gilleshenrard/leany/firmware/hardware/imu/bmi270/mems_bmi270.c

/*
 * SPDX-FileCopyrightText: 2025 Gilles Henrard <contact@gilleshenrard.com>
 *
 * SPDX-License-Identifier: MIT
 */

/**
 * @file mems_bmi270.c
 * @brief Implement the behavior of the BMI270 MEMS
 *
 * @author Gilles Henrard
 *
 * @details Datasheet : https://www.bosch-sensortec.com/media/boschsensortec/downloads/datasheets/bst-bmi270-ds000.pdf 
 */

#if IMU_MODEL == IMU_BMI270

#include <FreeRTOS.h>  //NOLINT(*-include-cleaner)
#include <bmi270.h>
#include <bmi2_defs.h>
#include <main.h>
#include <portmacro.h>
#include <projdefs.h>
#include <stdint.h>
#include <stm32f103xb.h>
#include <stm32f1xx_hal.h>
#include <stm32f1xx_ll_gpio.h>
#include <stm32f1xx_ll_spi.h>

#include "errorstack.h"
#include "hal_spi.h"
#include "imu.h"
#include "mahony.h"
#include "systick.h"

enum : uint8_t {
    kNBpositionRegisters = 16U,    ///< Number of registers holding Accelerometer and Gyroscope data
    kNBTemperatureRegisters = 2U,  ///< Number of registers holding Temperature data
    kConfigCheckAttempts = 3U,     ///< Maximum number of attempts to re-read a correct config file
};

/**
 * Timings in milliseconds
 */
typedef enum : uint16_t {
    kTimeoutMS = 1000U,           ///< Max number of milliseconds to wait for the device ID
    kConfigTimeoutMS = 20U,       ///< Max number of milliseconds after which the configuration should be ok
    kTemperatureRefreshMS = 10U,  ///< Number of milliseconds between temperature value refreshes
} Timing;

/**
 * Enumeration of the IDs of the functions used by the BMI270 implementation
 */
typedef enum : uint8_t {
    kBMI270readRegisters = 2,        ///< readRegisters() : Function reading several registers
    kBMI270writeRegisters = 3,       ///< burstWriteRegisters() : Function writing multiple registers
    kBMI270stateStartup = 4,         ///< stateStartup() : State in which the startup time is waited for
    kBMI270stateInitialising = 5,    ///< stateInitialising() : State in which the BMI270 is being initialised
    kBMI270checkCommunication = 7,   ///< checkSPICommunication() : Check the SPI communication with the BMI270
    kBMI270checkConfiguration = 8,   ///< checkConfigurationFile() : Check if written configuration file is correct
    kBMI270stateConfiguring = 9,     ///< stateConfiguring() : State in which the BMI270 is configured for the app.
    kBMI270stateMeasuring = 10,      ///< stateMeasuring() : State in which measurements are received from the BMI270
    kBMI270readTemperature = 11,     ///< readTemperature() : Function reading the BMI270 internal temp. registers
    kBMI270stateSelfTestAccel = 12,  ///< stateSelfTestingAccelerometer() : State in which the chip self-tests the acc.
    kBMI270stateSelfTestGyro = 13,   ///< stateSelfTestingGyro() : State in which the BMI270 self-tests the gyroscope
    kBMI270runAccelSelfTest = 14,    ///< runAccelerometerSelfTest() : Run the self-test command on the BMI270
    kBMI270configureRegisters = 15,  ///< configureRegisters() : Write an array of register number/value pairs
    kIMUsoftReset = 16,              ///< IMUsoftReset() function
} FunctionCode;

/**
 * @brief Union regrouping 8-bits and 16-bits arrays
 * @details
 *  This allows reading all the accelerometer and gyroscope values at once, and convert them to 16 bit instantly
 */
typedef union {
    uint8_t registers8bits[kNBpositionRegisters];                   ///< 8-bits registers array
    int16_t values16bits[((uint8_t)(kNBpositionRegisters) >> 1U)];  ///< 16-bits values array
} RawValues;

_Static_assert(((uint8_t)kNBpositionRegisters & (kNBpositionRegisters - 1U)) == 0,
               "NB_POSITION_REGISTERS must be an even number");

typedef uint8_t BMI270register;  ///< type definition for BMI270 registers

// Read/Write bit value
static constexpr uint16_t kConfigFileSize = 8192U;         ///< Size of the config file in bytes
static constexpr BMI270register kBMIwrite = 0x00U;         ///< Address byte value for a write operation
static constexpr BMI270register kBMIread = 0x80U;          ///< Address byte value for a read operation
const uint32_t kMaxSensorTimeTicks = 0xFFFFFFU;            ///< The maximum tick value before it wraps around to 0
const float kSensorTimeResolutionSeconds = 0.0000390625F;  ///< How many seconds a tick lasts

// Utility functions
static ErrorCode writeConfigurationFile(void);
static ErrorCode checkConfigurationFile(void);
static ErrorCode readTemperature(float* temperature_celsius);
static ErrorCode runAccelerometerSelfTest(RawValues* values_read, uint8_t positive_sign);
static inline uint32_t toTicks(const uint8_t registers[3]);
static void applyTemperatureDrift(float temperature_celcius, float accelerometer_g[3], float gyroscope_radps[3]);

/**
 * Accelerometer nominal sensitivity ratio from LSB to G, at +-2G range and 25°C
 * @details Equation :
 * Value(G) = Value(LSB) / 16384(LSB/G)
 *
 * See datasheet p. 12, section "Sensitivity"
 */
static constexpr float kNominalAccelLSBto2G = (1.0F / (float)BMI2_ACC_FOC_2G_REF);

/**
 * Accelerometer nominal sensitivity ratio from LSB to G, at +-16G range and 25°C
 * @details Equation :
 * Value(G) = Value(LSB) / 2048(LSB/G)
 *
 * See datasheet p. 12, section "Sensitivity"
 */
static constexpr float kNominalAccelLSBto16G = (1.0F / (float)BMI2_ACC_FOC_16G_REF);

/**
 * Gyroscope nominal sensitivity ratio from LSB to rad/s, at +-125°/s range and 25°C
 * @details Equation :
 * Value(rad/s) = (Value(LSB) / 262,144(LSB/dps)) * (PI/180°)
 *
 * See datasheet p. 14, section "Sensitivity"
 */
static constexpr float kNominalGyroLSBtoRadps = (1.0F / 262.144F) * 0.017453293F;

/**
 * Accelerometer temperature drift in [%/K], divided by 100 because percents
 */
static constexpr float kAccelTemperatureDriftPercentPerKelvin = (0.004F / 100.0F);

/**
 * Gyroscope temperature drift in [%/K], divided by 100 because percents
 */
static constexpr float kGyroTemperatureDriftPercentPerKelvin = (0.02F / 100.0F);

/**
 * Temperature in [°C] at which the internal temperature value read is 0x0000
 */
static constexpr float kReferenceTemperatureCelsius = 23.0F;

//external variables
extern const uint8_t bmi270_config_file[];  ///< BMI270 config file provided by Bosch Sensortec, declared in bmi270.c

//state variables
static uint8_t configfile_written = 0;  ///< Flag used to ensure config is written only once after reset
static ErrorCode result;                ///< Variable used to store error codes
static SPI spi_descriptor = {.handle = SPI1,
                             .cs_port = IMU_CS_GPIO_Port,
                             .pin = IMU_CS_Pin,
                             .highest_register_number = (BMI2_CMD_REG_ADDR + 1U),
                             .read_mask = kBMIread,
                             .write_mask = kBMIwrite,
                             .read_dummy = 1};  ///< Descriptor of the SPI port used

/****************************************************************************************************************/
/****************************************************************************************************************/

/**
 * Check whether the correct device ID can be retrieved
 *
 * @retval 0 Success
 * @retval 1 Error while reading the BMI270_CHIP_ID register
 * @retval 2 Incorrect device ID
 */
ErrorCode IMUcheckDeviceID(void) {
    BMI270register device_id = 0;

    LL_SPI_Enable(spi_descriptor.handle);

    //attempt to read a correct device ID for max. 1 second
    uint32_t first_tick = getCurrentTick();
    do {
        //store the bitwise-NOT value of the chip ID to make sure every bit is changed by the read command
        device_id = (BMI270register) ~((BMI270register)BMI270_CHIP_ID);

        //read the register
        result = readRegisters(&spi_descriptor, BMI2_CHIP_ID_ADDR, &device_id, 1);
        EXIT_ON_ERROR(result, kBMI270checkCommunication, 1)
    } while ((device_id != BMI270_CHIP_ID) && !systickTimeout(first_tick, kTimeoutMS));

    //check the device ID
    if (device_id != BMI270_CHIP_ID) {
        return (createErrorCode(kBMI270checkCommunication, 2, kErrorCritical));
    }

    return kSuccessCode;
}

/**
 * Request the IMU soft reset
 *
 * @retval 0 Success
 * @retval 1 Error while requesting the soft reset
 * @retval 2 Error while disabling the advanced power mode
 */
ErrorCode IMUsoftReset(void) {
    //issue a soft reset command to reset all registers to their default value
    // (useful when debugging and the supply voltage is not interrupted)
    BMI270register value = BMI2_SOFT_RESET_CMD;
    result = writeRegisters(&spi_descriptor, BMI2_CMD_REG_ADDR, &value, 1);
    EXIT_ON_ERROR(result, kIMUsoftReset, 1)

    //Disable advanced power mode
    value = 0x00;
    result = writeRegisters(&spi_descriptor, BMI2_PWR_CONF_ADDR, &value, 1);
    EXIT_ON_ERROR(result, kIMUsoftReset, 2)

    //Getting out of advanced power mode takes up to 450us
    vTaskDelay(pdMS_TO_TICKS(1U));

    configfile_written = 0;
    return kSuccessCode;
}

/**
 * State in which the BMI270 self-tests the accelerometer
 *
 * @details This follows the procedure descripted in the datasheet :
 * https://www.bosch-sensortec.com/media/boschsensortec/downloads/datasheets/bst-bmi270-ds000.pdf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
 * 
 * @retval 0 Success
 * @retval 1 Error while writing preliminary self-test configuration
 * @retval 2 Error while performing the positive-sign self-test
 * @retval 3 Error while performing the negative-sign self-test
 * @retval 4 Error while disabling the self-test
 * @retval 5 Self-test value deltas do not match the ones stated in the datasheet
 */
ErrorCode selfTestAccelerometer(void) {
    const BMI270register accel_range_register_number = 0x41U;  ///< Accelerometer range value register number
    BMI270register value = 0;

    const BMI270register configuration[][2] = {
        // NOLINTBEGIN(*-signed-bitwise)
        {BMI2_PWR_CTRL_ADDR, BMI2_ACC_EN_MASK},             //enable accelerometer
        {accel_range_register_number, BMI2_ACC_RANGE_16G},  //set the accel. range to +-16G
        {BMI2_ACC_SELF_TEST_ADDR, (1U << (uint8_t)BMI2_ACC_SELF_TEST_AMP_POS)},
        {BMI2_ACC_CONF_ADDR, (1U << BMI2_ACC_FILTER_PERF_MODE_POS) |
                                 (BMI270register)(BMI2_ACC_NORMAL_AVG4 << BMI2_ACC_BW_PARAM_POS) | BMI2_ACC_ODR_1600HZ},
        // NOLINTEND(*-signed-bitwise)
    };

    //send the configuration array
    const uint8_t nb_registers = sizeof(configuration) / 2;
    result = writeRegistersBunch(&spi_descriptor, configuration, nb_registers);
    EXIT_ON_ERROR(result, kBMI270stateSelfTestAccel, 1)

    //wait for 2ms
    vTaskDelay(pdMS_TO_TICKS(2U));

    RawValues lsb_posivite = {0};  ///< Buffer holding the LSB values read from the IC
    RawValues lsb_negative = {0};  ///< Buffer holding the LSB values read from the IC

    result = runAccelerometerSelfTest(&lsb_posivite, 1);
    EXIT_ON_ERROR(result, kBMI270stateSelfTestAccel, 2)

    result = runAccelerometerSelfTest(&lsb_negative, 0);
    EXIT_ON_ERROR(result, kBMI270stateSelfTestAccel, 3)

    //disable self-testing
    value = 0x00;
    result = writeRegisters(&spi_descriptor, BMI2_ACC_SELF_TEST_ADDR, &value, 1U);
    EXIT_ON_ERROR(result, kBMI270stateSelfTestAccel, 4)

    //transform the values read to values in [G] (9.81 m/s²)
    const float delta_x_g =
        (float)(lsb_posivite.values16bits[kXaxis] - lsb_negative.values16bits[kXaxis]) * kNominalAccelLSBto16G;
    const float delta_y_g =
        (float)(lsb_posivite.values16bits[kYaxis] - lsb_negative.values16bits[kYaxis]) * kNominalAccelLSBto16G;
    const float delta_z_g =
        (float)(lsb_posivite.values16bits[kZaxis] - lsb_negative.values16bits[kZaxis]) * kNominalAccelLSBto16G;

    //check if the minimum delta given in the datasheet is respected
    const float min_delta_x_g = 16.0F;
    const float min_delta_y_g = -15.0F;
    const float min_delta_z_g = 10.0F;
    if ((delta_x_g <= min_delta_x_g) || (delta_y_g >= min_delta_y_g) || (delta_z_g <= min_delta_z_g)) {
        return createErrorCode(kBMI270stateSelfTestAccel, 5, kErrorCritical);  // NOLINT(*-magic-numbers)
    }

    return kSuccessCode;
}

/**
 * State in which the BMI270 self-tests the gyroscope
 *
 * @details This follows the procedure descripted in the datasheet :
 * https://www.bosch-sensortec.com/media/boschsensortec/downloads/datasheets/bst-bmi270-ds000.pdf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
 * 
 * @retval 0 Success
 * @retval 1 Error while requesting the self-test triggering
 * @retval 2 Error while reading the self-test result
 * @retval 3 Error while reading the self-test error code
 * @retval 4 Gyroscope self-test internal error @note Internal error code stored one layer lower
 */
ErrorCode selfTestGyroscope(void) {
    BMI270register value = 0;

    //set the gyro self-test trigger command
    value = BMI2_G_TRIGGER_CMD;
    result = writeRegisters(&spi_descriptor, BMI2_CMD_REG_ADDR, &value, 1);
    EXIT_ON_ERROR(result, kBMI270stateSelfTestGyro, 1)

    //wait for the self-test done flag
    uint32_t start_tick = getCurrentTick();
    do {
        result = readRegisters(&spi_descriptor, BMI2_GYR_SELF_TEST_AXES_ADDR, &value, 1);
    } while (!isError(result) && !systickTimeout(start_tick, kTimeoutMS) &&
             ((value & (uint8_t)BMI2_ACC_SELF_TEST_DONE_MASK) != BMI2_ACC_SELF_TEST_DONE_MASK));

    EXIT_ON_ERROR(result, kBMI270stateSelfTestGyro, 2)

    //check if all axis are flagged as ok
    const BMI270register gyro_gain_status_registernumber = 0x38;
    const BMI270register all_gyroscope_ok =
        (BMI2_ACC_X_OK_MASK | BMI2_ACC_Y_OK_MASK | BMI2_ACC_Z_OK_MASK |  // NOLINT(*-signed-bitwise)
         BMI2_ACC_SELF_TEST_DONE_MASK);                                  // NOLINT(*-signed-bitwise)
    if ((value & all_gyroscope_ok) != all_gyroscope_ok) {
        BMI270register trigger_status = 0;
        result = readRegisters(&spi_descriptor, gyro_gain_status_registernumber, &trigger_status, 1);
        EXIT_ON_ERROR(result, kBMI270stateSelfTestGyro, 3)

        result = createErrorCodeLayer1(kBMI270stateSelfTestGyro, value, trigger_status, kErrorCritical);
        return pushErrorCode(result, kBMI270stateSelfTestGyro, 4);  // NOLINT(*-magic-numbers)
    }

    return kSuccessCode;
}

/**
 * Write the BMI270 config file
 * @attention This is to be done only once after Power On Reset
 *
 * @retval 0 Success
 * @retval 1 Error while starting the config file load
 * @retval 2 Error while writing the config file
 * @retval 3 Error while ending the config file load
 * @retval 4 Error while requesting the BMI270 status
 * @retval 5 BMI270 status error
 */
ErrorCode IMUinitialise(void) {
    //make sure config file is written only once after POR or soft reset
    if (configfile_written) {
        return kSuccessCode;
    }

    const BMI270register start_configfile_load = 0x00U;
    const BMI270register finish_configfile_load = 0x01U;

    //Request configuration start
    BMI270register value = start_configfile_load;
    result = writeRegisters(&spi_descriptor, BMI2_INIT_CTRL_ADDR, &value, 1);
    EXIT_ON_ERROR(result, kBMI270stateInitialising, 1)

    result = writeConfigurationFile();
    EXIT_ON_ERROR(result, kBMI270stateInitialising, 2)

    //Request configuration finish
    value = finish_configfile_load;
    result = writeRegisters(&spi_descriptor, BMI2_INIT_CTRL_ADDR, &value, 1);
    EXIT_ON_ERROR(result, kBMI270stateInitialising, 3)

    //Applying the new config takes up to 20ms
    vTaskDelay(pdMS_TO_TICKS(kConfigTimeoutMS));

    //Wait for the initialisation status register to show a success or an error
    uint32_t config_start_tick = getCurrentTick();
    do {
        result = readRegisters(&spi_descriptor, BMI2_INTERNAL_STATUS_ADDR, &value, 1);
        EXIT_ON_ERROR(result, kBMI270stateInitialising, 4)
    } while ((value == BMI2_NOT_INIT) && !systickTimeout(config_start_tick, kConfigTimeoutMS));

    //check if an initialisation error occurred
    if (value != BMI2_INIT_OK) {
        return createErrorCodeLayer1(kBMI270stateInitialising, 5, value, kErrorCritical);  // NOLINT(*-magic-numbers)
    }

    configfile_written = 1;
    return kSuccessCode;
}

/**
 * Configure the BMI270 registers for this application
 *
 * @retval 0 Success
 * @retval 1 Error while writing the configuration registers
 */
ErrorCode IMUconfigure(void) {
    const BMI270register accel_range_register_number = 0x41U;  ///< Accelerometer range value register number
    const BMI270register gyro_range_register_number = 0x43U;   ///< Gyroscope range value register number
    const BMI270register no_fifo = 0x00;                       ///< Value used to disable the FIFO

    const BMI270register configuration[][2] = {
        // NOLINTBEGIN(*-signed-bitwise)
        {BMI2_PWR_CTRL_ADDR,
         (BMI2_GYR_EN_MASK | BMI2_ACC_EN_MASK | BMI2_TEMP_EN_MASK)},  //enable temp, gyroscope and accel.
        {BMI2_ACC_CONF_ADDR, (BMI2_ACC_FILTER_PERF_MODE_MASK | (BMI2_ACC_CIC_AVG8 << 4U) | BMI2_ACC_ODR_1600HZ)},  //
        {accel_range_register_number, BMI2_ACC_RANGE_2G},  //set the accel. range to +-2G
        {BMI2_GYR_CONF_ADDR, (BMI2_GYR_FILTER_PERF_MODE_MASK | BMI2_GYR_NOISE_PERF_MODE_MASK |
                              (BMI2_GYR_NORMAL_MODE << 4U) | BMI2_GYR_ODR_1600HZ)},
        {gyro_range_register_number, BMI2_GYR_RANGE_125},  //set the gyroscope range to +-500°/s
        {BMI2_FIFO_CONFIG_1_ADDR, no_fifo},                //disable the FIFO (streaming mode)
        {BMI2_INT_MAP_DATA_ADDR, BMI2_DRDY_INT},           //enable Data Ready interrupt on INT1
        {BMI2_INT1_IO_CTRL_ADDR, BMI2_INT_OUTPUT_EN_MASK | BMI2_INT_OPEN_DRAIN_MASK |
                                     BMI2_INT_LEVEL_MASK},  //enable INT1 active high, open drain
        {BMI2_PWR_CONF_ADDR, 0x00},                         //disable advanced power mode
        // NOLINTEND(*-signed-bitwise)
    };

    //send the configuration array
    result = writeRegistersBunch(&spi_descriptor, configuration, (sizeof(configuration) / sizeof(configuration)[0]));
    EXIT_ON_ERROR(result, kBMI270stateConfiguring, 1)

    return kSuccessCode;
}

/**
 * Initialise the time fields of the Mahony filter's context
 *
 * @param[out] filter_context Mahony filter's current context
 */
void IMUsetupTimebase(MahonyContext* filter_context) {
    filter_context->dt.max_tick = kMaxSensorTimeTicks;
    filter_context->dt.tick_period_seconds = kSensorTimeResolutionSeconds;
}

/**
 * Get the latest IMU sample
 *
 * @param[out] sample Sample to gather
 * @retval 0 Success
 * @retval 1 Error while reading the sample registers
 * @retval 2 Error while reading the chip temperature
 */
ErrorCode IMUgetSample(IMUsample* sample) {
    RawValues lsb_values = {0};        ///< Buffer holding the LSB values read from the IC
    float temperature_celsius = 0.0F;  ///< Latest internal temperature in [°C]

    //read all accelerometer/gyroscope values
    result = readRegisters(&spi_descriptor, BMI2_ACC_X_LSB_ADDR, lsb_values.registers8bits, kNBpositionRegisters);
    EXIT_ON_ERROR(result, kBMI270stateMeasuring, 1)

    //apply the nominal sensitivity to the measurements to change them to usable units
    for (uint8_t axis = 0; axis < (uint8_t)kNBaxis; axis++) {
        sample->accelerometer_g[axis] = (float)(lsb_values.values16bits[axis]) * kNominalAccelLSBto2G;
        sample->gyroscope_radps[axis] = (float)(lsb_values.values16bits[axis + kNBaxis]) * kNominalGyroLSBtoRadps;
    }

    //read the BMI270 temperature every 10ms
    static TickType_t latest_temperature_tick = 0;
    if (systickTimeout(latest_temperature_tick, kTemperatureRefreshMS)) {
        latest_temperature_tick = getCurrentTick();

        result = readTemperature(&temperature_celsius);
        EXIT_ON_ERROR(result, kBMI270stateMeasuring, 2)
    }

    //take temperature drift into account with sensitivity
    applyTemperatureDrift(temperature_celsius, sample->accelerometer_g, sample->gyroscope_radps);

    //update the current sensor time ticks
    const uint8_t nb_measure_registers = (uint8_t)kNBaxis << 2U;
    sample->tick = toTicks(&lsb_values.registers8bits[nb_measure_registers]);

    return kSuccessCode;
}

/**
 * Get the number of samples to ignore after configuration
 *
 * @return 0 
 */
uint8_t getNbSamplesToIgnore(void) { return 0; }

/****************************************************************************************************************/
/****************************************************************************************************************/

/**
 * Write the configuration file to the BMI270 and check it is correct
 *
 * @retval 0 Success
 * @retval 1 Error while writing the config file
 * @retval 2 The Config file was not written correctly
 */
static ErrorCode writeConfigurationFile(void) {
    //Write the config file provided by Bosch Sensortec
    result = writeRegisters(&spi_descriptor, BMI2_INIT_DATA_ADDR, bmi270_config_file, kConfigFileSize);
    EXIT_ON_ERROR(result, kBMI270stateInitialising, 1)

    //re-read the configuration file written to make sure it is correct (max. 3 attempts)
    uint8_t attempts = kConfigCheckAttempts;
    do {
        result = checkConfigurationFile();
    } while ((--attempts) && isError(result));
    EXIT_ON_ERROR(result, kBMI270stateInitialising, 2)

    return result;
}

/**
 * Read the configuration file stored in the BMI270 and make sure it corresponds to the one provided by Bosch
 * 
 * @retval 0 Success
 * @retval 1 Timeout while reading the configuration file
 * @retval 2 Data difference between configuration files
 */
static ErrorCode checkConfigurationFile(void) {
    const uint8_t spi_rx_filler = 0xFFU;  ///< Value to send as a filler while receiving multiple bytes

    //set timeout timer and enable CS
    uint32_t spi_start_tick = getCurrentTick();
    LL_GPIO_ResetOutputPin(IMU_CS_GPIO_Port, IMU_CS_Pin);

    //send the config data read request and receive a dummy byte
    (void)receiveSPIbyte(&spi_descriptor, BMI2_INIT_DATA_ADDR, spi_start_tick);
    (void)receiveSPIbyte(&spi_descriptor, spi_rx_filler, spi_start_tick);

    //receive the bytes to read
    uint8_t failure = 0;
    uint16_t byte_index = 0;
    do {
        BMI270register value = receiveSPIbyte(&spi_descriptor, spi_rx_filler, spi_start_tick);
        failure = (value != bmi270_config_file[byte_index]);
        byte_index++;
    } while (!failure && (byte_index < kConfigFileSize) && !systickTimeout(spi_start_tick, kSPItimeoutMS));

    //wait for transaction to be finished and clear Overrun flag
    while (LL_SPI_IsActiveFlag_BSY(spi_descriptor.handle) && !systickTimeout(spi_start_tick, kSPItimeoutMS)) {
    };
    LL_SPI_ClearFlag_OVR(spi_descriptor.handle);

    //disable CS
    LL_GPIO_SetOutputPin(IMU_CS_GPIO_Port, IMU_CS_Pin);

    //if timeout, error
    if (systickTimeout(spi_start_tick, kSPItimeoutMS)) {
        return (createErrorCode(kBMI270checkConfiguration, 1, kErrorWarning));
    }

    if (failure || (byte_index < kConfigFileSize)) {
        return (createErrorCode(kBMI270checkConfiguration, 2, kErrorWarning));
    }

    return kSuccessCode;
}

/**
 * Read the BMI270 internal temperature
 * 
 * @param[out] temperature_celsius Temperature in [°C] to update if the temperature read is valid
 * @retval 0 Success
 * @retval 1 Error while reading the registers
 */
static ErrorCode readTemperature(float* temperature_celsius) {
    int16_t read_buffer = 0x0000;

    //read temperature value
    result = readRegisters(&spi_descriptor, BMI2_TEMPERATURE_0_ADDR, (uint8_t*)&read_buffer, kNBTemperatureRegisters);
    EXIT_ON_ERROR(result, kBMI270readTemperature, 1)

    //check if the temperature LSB read is valid
    const int16_t invalid_temperature_lsb = (int16_t)0x8000;
    if (read_buffer == invalid_temperature_lsb) {
        return kSuccessCode;
    }

    //transform temperature LSB to °C
    const float kelvin_per_lsb = 0.001953125F;
    *temperature_celsius = kReferenceTemperatureCelsius + ((float)read_buffer * kelvin_per_lsb);

    return kSuccessCode;
}

/**
 * Send the self-test request to the BMI270 and read its results
 * 
 * @param[out] values_read Buffer to which save the read self-test values 
 * @param positive_sign 1 if self-test sign is positive, 0 if negative
 * @retval 0 Success
 * @retval 1 Error while sending the self-test request
 * @retval 2 Error while reading the self-test results
 */
static ErrorCode runAccelerometerSelfTest(RawValues* values_read, uint8_t positive_sign) {
    //prepare the register value to write to start the self-testing
    BMI270register value = (uint8_t)(positive_sign << (uint8_t)BMI2_ACC_SELF_TEST_SIGN_POS);
    value |= (1U << (uint8_t)BMI2_ACC_SELF_TEST_AMP_POS);
    value |= (uint8_t)BMI2_ACC_SELF_TEST_EN_MASK;

    //write the self-test request and wait for it to finish
    result = writeRegisters(&spi_descriptor, BMI2_ACC_SELF_TEST_ADDR, &value, 1U);
    EXIT_ON_ERROR(result, kBMI270runAccelSelfTest, 1)
    vTaskDelay(pdMS_TO_TICKS(51U));

    //read all accelerometer/gyroscope values
    result = readRegisters(&spi_descriptor, BMI2_ACC_X_LSB_ADDR, values_read->registers8bits, kNBpositionRegisters);
    EXIT_ON_ERROR(result, kBMI270runAccelSelfTest, 2)

    return kSuccessCode;
}

/**
 * Assemble sensor time registers into tick value
 *
 * @param registers Sensor time registers
 * @return Tick value
 */
static inline uint32_t toTicks(const uint8_t registers[3]) {
    return (registers[0] | (uint32_t)(registers[1U] << 8U)  //NOLINT (*-magic-numbers)
            | (uint32_t)(registers[2] << 16U));             //NOLINT (*-magic-numbers)
}

/**
 * Apply temperature drifts to the measurements
 *
 * @param temperature_celcius Internal temperature in [°C]
 * @param[out] accelerometer_g Accelerometer values in [G] (9.81 m/s²)
 * @param[out] gyroscope_radps Gyroscope values in [rad/s]
 */
//NOLINTNEXTLINE(bugprone-easily-swappable-parameters)
static void applyTemperatureDrift(const float temperature_celcius, float accelerometer_g[3], float gyroscope_radps[3]) {
    const float delta_celsius = temperature_celcius - kReferenceTemperatureCelsius;
    const float accel_drift_percent = (delta_celsius * kAccelTemperatureDriftPercentPerKelvin);
    const float gyro_drift_percent = (delta_celsius * kGyroTemperatureDriftPercentPerKelvin);

    for (uint8_t axis = 0; axis < (uint8_t)kNBaxis; axis++) {
        accelerometer_g[axis] += (accel_drift_percent * accelerometer_g[axis]);
        gyroscope_radps[axis] += (gyro_drift_percent * gyroscope_radps[axis]);
    }
}
#endif
