gilleshenrard/leany/firmware/tasks/task_battery.c

/**
 * SPDX-FileCopyrightText: 2026 Gilles Henrard <contact@gilleshenrard.com>
 * SPDX-License-Identifier: MIT
 *
 * @file task_battery.c
 * @brief Implement the battery voltage and charger status monitoring
 * @author Gilles Henrard
 */
#include "task_battery.h"

#include <FreeRTOS.h>
#include <FreeRTOSConfig.h>
#include <assert.h>
#include <main.h>
#include <portmacro.h>
#include <projdefs.h>
#include <semphr.h>
#include <stdint.h>
#include <stm32f103xb.h>
#include <stm32f1xx_ll_i2c.h>
#include <task.h>

#include "bq25619.h"
#include "bq25619_registers.h"
#include "errorstack.h"
#include "hal_adc.h"
#include "hal_i2c.h"
#include "hardware_events.h"
#include "systick.h"
#include "task_gpio.h"

enum : uint16_t {
    kStackSize_words = 110U,         ///< Amount of words in the task stack
    kTaskLowPriority = 3U,           ///< FreeRTOS number for a low priority task
    kNbChipIDtests = 5U,             ///< Number of times chip ID reading must be tested
    kBatteryFullPercent = 100U,      ///< Value used as a 100% battery level
    kNbRetries = 5U,                 ///< Maximum number of retries upon I²C lack of ACK
    kNbAverageSamples = 16U,         ///< Maximum number of elements in the average buffer
    kAdcMaxValue = 4095U,            ///< Maximum ADC LSB value (12-bits -> [0 ... 4095])
    kBatteryMaxMv = 4200U,           ///< Maximum voltage of a typical lithium cell in [mV]
    kBatteryMinMv = 3500U,           ///< Minimum voltage of a typical lithium cell in [mV]
    kBatteryMinDetectionMv = 2500U,  ///< Minimum voltage detection threshold in [mV]
    kNbBatteryLevelSteps = 21U,      ///< Number of battery level steps in the lookup table
    kBatteryLevelPercentStep = 5U,   ///< Number of percents between two steps
};

static_assert(((uint8_t)kNbAverageSamples & ((uint8_t)kNbAverageSamples - 1U)) == 0U,
              "kNbAverageSamples must be a power of 2");

/**
 * Timings in milliseconds
 */
typedef enum : uint16_t {
    kBatteryLvlUpdatePeriodMs = 1000U,  ///< Period in [ms] between two battery level updates
    kMutexTimeoutMs = 10U,              ///< Maximum number of milliseconds before considering a mutex timeout
    kChipIDtimeout = 1000U,             ///< Maximum number of milliseconds to attempt reading the chip ID
    kUpdatePeriodMS = 200U,             ///< Period between two status updates in [ms]
    kMutexMS = 5U,                      ///< Max number of milliseconds to wait for a mutex
} Timing;

/**
 * @brief Enumeration of all the function ID used in errors
 */
typedef enum : uint8_t {
    kTaskLoop = 1,          ///< taskBatteryManagement() function
    kStateStartup = 3,      ///< stateStartup() state function
    kStateIdle = 4,         ///< stateIdle() state function
    kRequestRead = 5,       ///< requestRead() function
    kStateConfiguring = 8,  ///< stateConfiguring() state function
} FunctionCode;

//state machine functions
static void taskBatteryManagement(void* argument);
static ErrorCode stateStartup(void);
static ErrorCode stateConfiguring(void);
static ErrorCode stateIdle(void);
static void updateBatteryVoltage(void);
static uint16_t adcToBatteryVoltage_mV(uint16_t adc_raw, uint32_t adc_vref_mv);
static void averageBatteryVoltageMv(uint32_t new_voltage_mv);
static uint8_t batteryVoltageToPercent(uint32_t voltage_mv);

/**
 * Lookup table mapping SoC level (in 5% steps) to cell voltage (mV).
 *
 * Index 0  = 0%   SoC = 3500 mV  (discharge cutoff)
 * Index 20 = 100% SoC = 4200 mV  (fully charged)
 *
 * Based on a typical Li-ion 18650 OCV discharge curve at ~80 mA load.
 * Voltage range: 3500 mV to 4200 mV.
 * Step size: 5% SoC per entry.
 */
static constexpr uint16_t kBatteryLevelsLookupTable[kNbBatteryLevelSteps] = {
    kBatteryMinMv,  // 0%
    3520U,          // 5%
    3550U,          // 10%
    3580U,          // 15%
    3610U,          // 20%
    3630U,          // 25%
    3650U,          // 30%
    3670U,          // 35%
    3690U,          // 40%
    3710U,          // 45%
    3730U,          // 50%
    3760U,          // 55%
    3790U,          // 60%
    3820U,          // 65%
    3860U,          // 70%
    3910U,          // 75%
    3970U,          // 80%
    4030U,          // 85%
    4090U,          // 90%
    4150U,          // 95%
    kBatteryMaxMv,  // 100%
};

// NOLINTBEGIN (hicpp-use-nullptr)
static volatile TaskHandle_t task_handle = nullptr;              ///< handle of the FreeRTOS task
static volatile FunctionCode state = kStateStartup;              ///< Current state machine state
static StackType_t task_stack[kStackSize_words] = {0};           ///< Buffer used as the task stack
static StaticTask_t task_state = {0};                            ///< Task state variables
static SemaphoreHandle_t battery_mutex = nullptr;                ///< Mutex used to protect the battery status
static ErrorCode result = {0};                                   ///< Buffer used to store the latest error code
static I2C_TypeDef* i2c_handle = I2C1;                           ///< I²C handle to use with all transmissons
static uint8_t battery_percentage = kBatteryFullPercent;         ///< Current battery percentage
static uint8_t previous_battery_percentage = 0;                  ///< Previous battery percentage
static bool battery_charging = false;                            ///< Current battery charge status
static TickType_t previous_tick = 0;                             ///< Tick at the last status update
static ChargerStatus current_battery_status;                     ///< Current battery status flags
static uint32_t last_battery_lvl_update_tick = 0;                ///< Last tick at which battery lvl was updated
static uint32_t battery_average_queue[kNbAverageSamples] = {0};  ///< Buffer used for averaging battery
static uint8_t battery_average_nbsamples = 0;                    ///< Number of samples saved in the buffer
static uint8_t battery_average_index = 0;                        ///< Index of the current buffer head
static uint32_t battery_average_total = 0;                       ///< Total value used to calculate battery average
static uint16_t battery_voltage_mv = 0;                          ///< Current battery voltage in [mV]
// NOLINTEND

/****************************************************************************************************************/
/****************************************************************************************************************/

/**
 * Create the FreeRTOS task which takes care of the battery and charger management
 *
 * @return Success
 */
ErrorCode createBatteryTask(void) {
    // NOLINTBEGIN (hicpp-use-nullptr)
    static StaticSemaphore_t battery_mutex_state = {0};  ///< battery mutex state variables
    // NOLINTEND

    //create a semaphore to protect battery status
    battery_mutex = xSemaphoreCreateMutexStatic(&battery_mutex_state);
    configASSERT(battery_mutex);

    //create the static task
    task_handle = xTaskCreateStatic(taskBatteryManagement, "Battery management task", kStackSize_words, nullptr,
                                    kTaskLowPriority, task_stack, &task_state);
    if (!task_handle) {
        Error_Handler();
    }

    return kSuccessCode;
}

/**
 * Get the battery status
 *
 * @param[out] status Battery current status
 * @return Success 
 */
//NOLINTNEXTLINE(bugprone-easily-swappable-parameters)
ErrorCode getBatteryStatus(BatteryStatus* status) {
    if (!status) {
        return createErrorCode(1, 1, kErrorError);
    }

    if (xSemaphoreTake(battery_mutex, pdMS_TO_TICKS(kMutexTimeoutMs)) != pdTRUE) {
        return createErrorCode(1, 2, kErrorError);
    }

    *status = (BatteryStatus){.level_percents = battery_percentage,
                              .charging = (battery_charging || isBQ25619charging(&current_battery_status))};
    xSemaphoreGive(battery_mutex);
    return kSuccessCode;
}

/**
 * Set the battery charge status
 * @param status New status
 */
void setBatteryChargeStatus(bool status) {
    if (xSemaphoreTake(battery_mutex, pdMS_TO_TICKS(kMutexTimeoutMs)) == pdTRUE) {
        battery_charging = status;
        xSemaphoreGive(battery_mutex);
    }
}

/**
 * Turn the system off
 *
 * @return disconnectBattery() code
 */
ErrorCode turnSystemOff(void) { return disconnectBattery(); }

/**
 * Get the latest measured battery voltage
 *
 * @param[out] voltage_mv Battery voltage in [mV]
 * @retval true Successfully retrieved
 * @retval false Could not retrieve voltage
 */
bool getBatteryVoltageMv(uint16_t* voltage_mv) {
    bool success = false;
    if (xSemaphoreTake(battery_mutex, pdMS_TO_TICKS(kMutexMS)) == pdTRUE) {
        *voltage_mv = battery_voltage_mv;
        success = true;
        xSemaphoreGive(battery_mutex);
    }

    return success;
}

/****************************************************************************************************************/
/****************************************************************************************************************/

/**
 * Run the battery management FreeRTOS task
 *
 * @param argument Unused
 */
static void taskBatteryManagement(void* argument) {
    (void)argument;

    LL_I2C_Enable(i2c_handle);

    last_battery_lvl_update_tick = getCurrentTick();
    while (1) {
        switch (state) {
            case kStateStartup:
                result = stateStartup();
                state = kStateConfiguring;
                break;

            case kStateConfiguring:
                result = stateConfiguring();
                previous_tick = getCurrentTick();
                state = kStateIdle;
                break;

            case kStateIdle:
                result = stateIdle();
                break;

            case kTaskLoop:
            case kRequestRead:
            default:
                result = createErrorCode(kTaskLoop, 1, kErrorCritical);
                break;
        }

        if (isError(result)) {
            Error_Handler();
        }
    }
}

/**
 * State during which the charger startup procedure is ran
 *
 * @retval 0 Success
 * @retval 1 Error while reading the chip ID
 * @retval 2 Invalid chip ID
 * @retval 3 Error while resetting the registers to default
 */
static ErrorCode stateStartup(void) {
    result = testBQ25619identifier();
    EXIT_ON_ERROR(result, kStateStartup, 1)

    for (uint8_t attempt = 0; attempt < kNbRetries; attempt++) {
        result = resetBQ25619();
        if (getDeepestError(result) != kErrorAcknowledgeFailure) {
            break;
        }
    }
    EXIT_ON_ERROR(result, kStateStartup, 2)

    vTaskDelay(pdMS_TO_TICKS(5));

    return kSuccessCode;
}

/**
 * State during which the charger's registers are configured
 *
 * @retval 0 Success
 * @retval 1 Error while writing a configuration register
 */
static ErrorCode stateConfiguring(void) {
    for (uint8_t attempt = 0; attempt < kNbRetries; attempt++) {
        result = configureBQ25619();
        if (getDeepestError(result) != kErrorAcknowledgeFailure) {
            break;
        }
    }
    EXIT_ON_ERROR(result, kStateConfiguring, 1)

    return kSuccessCode;
}

/**
 * State during which the state machine is idle
 *
 * @retval 1 Error while reading the status
 * @retval 2 Error while re-reading the status
 */
static ErrorCode stateIdle(void) {
    vTaskDelayUntil(&previous_tick, pdMS_TO_TICKS(kUpdatePeriodMS));

    ChargerStatus changes;

    //retrieve the latest charger status
    for (uint8_t attempt = 0; attempt < kNbRetries; attempt++) {
        result = updateBQ25619status(&current_battery_status, &changes);
        if (getDeepestError(result) != kErrorAcknowledgeFailure) {
            break;
        }
    }
    EXIT_ON_ERROR(result, kStateIdle, 1);

    //if status changed, trigger event
    if (BQ25619statusChanged(&changes)) {
        if (BQ25619Error(&current_battery_status)) {
            return createErrorCode(kStateIdle, 2, kErrorError);
        }
        triggerHardwareEvent(kEventBatteryStatus);
    }

    updateBatteryVoltage();

    uint16_t battery_voltage = 0;
    if (!getBatteryVoltageMv(&battery_voltage)) {
        return kSuccessCode;
    }

    //if battery voltage is too low, shut the system down
    if ((battery_voltage > kBatteryMinDetectionMv) && (battery_voltage <= kBatteryMinMv)) {
        turnSystemOff();
    }

    return kSuccessCode;
}

/**
 * Request a battery read on ADC
 */
static void updateBatteryVoltage(void) {
    static uint8_t updating = 0;

    //check if it is time to update the battery percentage
    if (systickTimeout(last_battery_lvl_update_tick, kBatteryLvlUpdatePeriodMs)) {
        last_battery_lvl_update_tick = getCurrentTick();
        updating = 1;
    }

    //if not supposed to be updating, exit
    if (!updating) {
        return;
    }

    //get the latest battery value
    uint16_t battery_adc_raw = 0;
    if (!getADCvalue(kADC1, kADCchannelBattery, &battery_adc_raw)) {
        return;  // ADC not ready yet, retry on next loop iteration
    }

    uint32_t adc_reference_mv = 0;
    if (!getADCreference_mV(&adc_reference_mv)) {
        updating = 0;
        return;
    }

    //transform the ADC value to [mV]
    uint16_t new_battery_voltage_mv = adcToBatteryVoltage_mV(battery_adc_raw, adc_reference_mv);
    averageBatteryVoltageMv(new_battery_voltage_mv);

    //transform battery voltage to percentage
    if (!getBatteryVoltageMv(&new_battery_voltage_mv)) {
        updating = 0;
        return;
    }

    const uint8_t new_percentage = batteryVoltageToPercent(new_battery_voltage_mv);
    if (xSemaphoreTake(battery_mutex, pdMS_TO_TICKS(kMutexMS)) != pdTRUE) {
        updating = 0;
        return;
    }

    battery_percentage = new_percentage;
    xSemaphoreGive(battery_mutex);

    if (new_percentage != previous_battery_percentage) {
        previous_battery_percentage = new_percentage;
        triggerHardwareEvent(kEventBatteryStatus);
    }

    updating = 0;
}

/**
 * Transform an ADC value to battery voltage in [mV]
 *
 * @param adc_raw Value to transform
 * @param adc_vref_mv ADC voltage reference in [mV]
 * @return Battery voltage in [mV]
 */
static uint16_t adcToBatteryVoltage_mV(uint16_t adc_raw, uint32_t adc_vref_mv) {
    static constexpr uint32_t kVoltageDividerHighKohms = 56UL;
    static constexpr uint32_t kVoltageDividerLowKohms = 56UL;

    if (!adc_vref_mv) {
        return 0;
    }

    const uint32_t conversion_numerator = (adc_vref_mv * (kVoltageDividerHighKohms + kVoltageDividerLowKohms));
    static constexpr uint32_t kConversionDenominator = (kAdcMaxValue * kVoltageDividerLowKohms);

    return (uint16_t)((adc_raw * conversion_numerator) / kConversionDenominator);
}

/**
 * Blend a new battery voltage into the running average measurements
 *
 * @param new_voltage_mv New voltage to add in [mV]
 */
static void averageBatteryVoltageMv(uint32_t new_voltage_mv) {
    //add elements to the buffer until it's full
    if (battery_average_nbsamples < kNbAverageSamples) {
        battery_average_queue[battery_average_index] = new_voltage_mv;
        battery_average_index++;
        battery_average_total += new_voltage_mv;
        battery_average_nbsamples++;
        if (xSemaphoreTake(battery_mutex, pdMS_TO_TICKS(kMutexMS)) == pdTRUE) {
            battery_voltage_mv = (uint16_t)(battery_average_total / battery_average_nbsamples);
            xSemaphoreGive(battery_mutex);
        }
        return;
    }

    //buffer is full, use a cyclic average
    battery_average_index %= kNbAverageSamples;  // 16 -> 0
    battery_average_total -= battery_average_queue[battery_average_index];
    battery_average_queue[battery_average_index] = new_voltage_mv;
    battery_average_total += new_voltage_mv;
    battery_average_index = (battery_average_index + 1U) % kNbAverageSamples;
    if (xSemaphoreTake(battery_mutex, pdMS_TO_TICKS(kMutexMS)) == pdTRUE) {
        battery_voltage_mv = (uint16_t)(battery_average_total / kNbAverageSamples);
        xSemaphoreGive(battery_mutex);
    }
}

/**
 * Transform a battery voltage to a percentage, following a typical cell curve
 *
 * @param voltage_mv Voltage to transform, in [mV]
 * @return Battery percentage
 */
static uint8_t batteryVoltageToPercent(uint32_t voltage_mv) {
    if (voltage_mv >= kBatteryMaxMv) {
        return kBatteryFullPercent;
    }

    if (voltage_mv <= kBatteryMinMv) {
        return 0;
    }

    uint8_t step = 0U;
    for (step = 0U; step < kNbBatteryLevelSteps; step++) {
        if (kBatteryLevelsLookupTable[step] >= voltage_mv) {
            break;
        }
    }

    return (uint8_t)(step * kBatteryLevelPercentStep);
}
