gilleshenrard/leany/firmware/tasks/task_imu.c

/*
 * SPDX-FileCopyrightText: 2025 Gilles Henrard <contact@gilleshenrard.com>
 *
 * SPDX-License-Identifier: MIT
 */

/**
 * @file task_imu.c
 * @brief Implement the generic IMU FreeRTOS task
 *
 * @author Gilles Henrard
 */
#include "task_imu.h"

#include <FreeRTOS.h>
#include <FreeRTOSConfig.h>
#include <main.h>
#include <math.h>
#include <portmacro.h>
#include <projdefs.h>
#include <semphr.h>
#include <stddef.h>
#include <stdint.h>
#include <task.h>

#include "errorstack.h"
#include "hardware_events.h"
#include "imu.h"
#include "mahony.h"
#include "orientation.h"
#include "task_serial.h"

enum : uint16_t {
    kStackSize_words = 110U,  ///< Amount of words in the task stack
    kTaskPriority = 5U,       ///< FreeRTOS number for a low priority task
};

/**
 * Timings in milliseconds
 */
typedef enum : uint16_t {
    kStartupTimeMS = 10U,  ///< Number of milliseconds to wait after a reset
    kTimeoutMS = 20U,      ///< Max number of milliseconds to wait for a notification
    kMutexMS = 100U,       ///< Max number of milliseconds to wait for a mutex
} Timing;

/**
 * Enumeration of the IDs of the functions used by the BMI270 implementation
 */
typedef enum : uint8_t {
    kFunctionTask = 1,      ///< taskIMU() : Function running the IMU state machine
    kStateStartup = 2,      ///< stateStartup() : State in which the IMU is restarted
    kstateConfiguring = 3,  ///< stateConfiguring() : State in which the IMU is being initialised
    kStateMeasuring = 4,    ///< stateMeasuring() : State in which measurements are received from the BMI270
    kIgnoreSamples = 5,     ///< ignoreSamples() : Function in which samples are ignored after configuration
    kSetOrientation = 6,    ///< setDisplayOrientation() : Function in which the screen orientation is set
    kgetOrientation = 7,    ///< getDisplayOrientation() : Function in which the screen orientation is retrieved
    kStateError = 8,        ///< State in which the IMU is in error mode
    kGetMahonyContext = 9,  ///< getMahonyContext(): Function in which the current context is retrieved
} FunctionCode;

// State machine functions
static void taskIMU(void* argument);
static ErrorCode stateStartup(void);
static ErrorCode stateConfiguring(void);
static ErrorCode ignoreSamples(void);
static ErrorCode stateMeasuring(void);

// Utility functions
static void consumeStateMachineError(ErrorCode code);

// constants
static constexpr float kRadiansToDegreesTenths = 572.957795F;   ///< One radian in tenths of degrees (= 10 * (180°/PI))
static constexpr float kDegreesTenthsToRadians = 0.001745329F;  ///< One tenth of degree in radians (= (180°/PI) / 10)

//state variables
static volatile TaskHandle_t task_handle = nullptr;    ///< handle of the FreeRTOS task
static SemaphoreHandle_t angles_mutex = nullptr;       ///< handle of the mutex used to protect angles measurements
static SemaphoreHandle_t orientation_mutex = nullptr;  ///< handle of the mutex used to protect display orientation
static Orientation current_orientation = kLandscape;   ///< Current screen orientation
static FunctionCode imu_state = kStateStartup;         ///< Current IMU state
static ErrorCode result;                               ///< Variable used to receive the functions' result codes
static volatile bool task_notifiable = false;  ///< Flag indicating whether the task is ready to treat notifications
static float angles_zeroing_rad[kNBaxis - 1] = {0, 0};  ///< Angles used to zero out the measurements
static bool holding = false;                            ///< Flag indicating whether the measurements are held
static bool zeroed = false;                             ///< Measurements zeroing status
static MahonyContext filter_context = {.base_ki = kIntegralGain,
                                       .base_kp = kProportionalGain,  // computed with 1/Tau
                                       .min_alignment_cosine = kMinAlignCosine,
                                       .max_norm_epsilon = kMaxNormEpsilon,
                                       .min_kp_trust_factor = kMinKpTrustFactor,
                                       .state.manual_pure_gyro = false};  ///< Current Mahony filter context

/****************************************************************************************************************/
/****************************************************************************************************************/

/**
 * Handle an INT1 or INT2 GPIO interrupt from the IMU
 *
 * @param interrupt_pin Pin which triggered the interrupt
 */
void IMUinterruptTriggered(uint8_t interrupt_pin) {
    BaseType_t has_woken = 0;

    // vPortEnterCritical();

    //if INT1, notify the IMU task
    if (task_notifiable && (interrupt_pin == 1)) {
        vTaskNotifyGiveFromISR(task_handle, &has_woken);
    }

    // vPortExitCritical();

    portYIELD_FROM_ISR(has_woken);
}

/**
 * Create the FreeRTOS static task taking care of the IMU sensor
 */
void createIMUtask(void) {
    // NOLINTBEGIN (hicpp-use-nullptr)
    static StackType_t task_stack[kStackSize_words] = {0};   ///< Buffer used as the task stack
    static StaticTask_t task_state = {0};                    ///< Task state variables
    static StaticSemaphore_t measure_mutex_state = {0};      ///< Angles value mutex state variables
    static StaticSemaphore_t orientatino_mutex_state = {0};  ///< orientation mutex state variables
    // NOLINTEND

    //create the static task
    task_handle =
        xTaskCreateStatic(taskIMU, "IMU task", kStackSize_words, nullptr, kTaskPriority, task_stack, &task_state);
    configASSERT(task_handle);

    //create a semaphore to protect mearurements
    angles_mutex = xSemaphoreCreateMutexStatic(&measure_mutex_state);
    configASSERT(angles_mutex);

    //create a semaphore to protect orientation
    orientation_mutex = xSemaphoreCreateMutexStatic(&orientatino_mutex_state);
    configASSERT(orientation_mutex);

    logSerial(kErrorInfo, "IMU task and angles mutex created");
}

/**
 * @brief Transpose a measurement to an angle in tenths of degrees with the Z axis
 *
 * @param axis Axis for which get the angle with the Z axis
 * @return Angle with the Z axis
 */
int16_t getAngleDegreesTenths(Axis axis) {
    if (xSemaphoreTake(angles_mutex, pdMS_TO_TICKS(kMutexMS)) == pdFALSE) {
        return 0;
    }

    float current_angle_rad = angleAlongAxis(&filter_context.attitude, axis);
    float total = (current_angle_rad + angles_zeroing_rad[axis]);

    (void)xSemaphoreGive(angles_mutex);
    return (int16_t)(total * kRadiansToDegreesTenths);
}

/**
 * @brief Set the measurements in relative mode and zero down the values
 */
void IMUzeroDown(void) {
    if (xSemaphoreTake(angles_mutex, pdMS_TO_TICKS(kMutexMS)) == pdFALSE) {
        return;
    }

    angles_zeroing_rad[kXaxis] = -angleAlongAxis(&filter_context.attitude, kXaxis);
    angles_zeroing_rad[kYaxis] = -angleAlongAxis(&filter_context.attitude, kYaxis);
    zeroed = true;

    (void)xSemaphoreGive(angles_mutex);
}

/**
 * @brief Set the measurements in absolute mode (no zeroing compensation)
 */
void IMUcancelZeroing(void) {
    if (xSemaphoreTake(angles_mutex, pdMS_TO_TICKS(kMutexMS)) == pdFALSE) {
        return;
    }

    angles_zeroing_rad[kXaxis] = 0.0F;
    angles_zeroing_rad[kYaxis] = 0.0F;
    zeroed = false;

    (void)xSemaphoreGive(angles_mutex);
}

/**
 * Check if the IMU has been zeroed (relative mode)
 *
 * @retval true IMU is in relative mode
 * @retval false IMU is in absolute mode 
 */
bool isIMUzeroed(void) {
    bool current_zeroing = false;

    if (xSemaphoreTake(angles_mutex, pdMS_TO_TICKS(kMutexMS)) == pdTRUE) {
        current_zeroing = zeroed;
        (void)xSemaphoreGive(angles_mutex);
    }

    return current_zeroing;
}

/**
 * Get the Mahony filter's Proportional value
 *
 * @return kP value
 */
float getIMU_KP(void) {
    float current_kp = 0.0F;

    if (xSemaphoreTake(angles_mutex, pdMS_TO_TICKS(kMutexMS)) == pdTRUE) {
        current_kp = filter_context.base_kp;
        (void)xSemaphoreGive(angles_mutex);
    }

    return current_kp;
}

/**
 * Get the Mahony filter's Integral value
 *
 * @return kI value
 */
float getIMU_KI(void) {
    float current_ki = 0.0F;

    if (xSemaphoreTake(angles_mutex, pdMS_TO_TICKS(kMutexMS)) == pdTRUE) {
        current_ki = filter_context.base_ki;
        (void)xSemaphoreGive(angles_mutex);
    }

    return current_ki;
}

/**
 * Set the Mahony filter's Integral value
 *
 * @param value Filter's integral value
 */
void setIMU_KI(float value) {
    if ((value < 0.0F) || isnan(value) || isinf(value)) {
        return;
    }

    if (xSemaphoreTake(angles_mutex, pdMS_TO_TICKS(kMutexMS)) == pdTRUE) {
        filter_context.base_ki = value;
        resetMahonyFilter(&filter_context);
        (void)xSemaphoreGive(angles_mutex);
    }
}

/**
 * Set the Mahony filter's Proportional value
 *
 * @param value Filter's Proportional value
 */
void setIMU_KP(float value) {
    if ((value < 0.0F) || isnan(value) || isinf(value)) {
        return;
    }

    if (xSemaphoreTake(angles_mutex, pdMS_TO_TICKS(kMutexMS)) == pdTRUE) {
        filter_context.base_kp = value;
        resetMahonyFilter(&filter_context);
        (void)xSemaphoreGive(angles_mutex);
    }
}

/**
 * Toggle the IMU measurements holding
 *
 * @return New Holding value
 */
bool toggleIMU_hold(void) {
    bool new_holding = false;
    if (xSemaphoreTake(angles_mutex, pdMS_TO_TICKS(kMutexMS)) == pdTRUE) {
        holding = (bool)!holding;
        new_holding = holding;
        (void)xSemaphoreGive(angles_mutex);
    }

    return new_holding;
}

/**
 * Get the current measurements holding status
 *
 * @retval 1 IMU is in hold mode
 * @retval 0 IMU is running normally
 */
bool isIMUmeasurementsHolding(void) {
    bool current_holding = false;

    if (xSemaphoreTake(angles_mutex, pdMS_TO_TICKS(kMutexMS)) == pdTRUE) {
        current_holding = holding;
        (void)xSemaphoreGive(angles_mutex);
    }

    return current_holding;
}

/**
 * Set whether the manual pure gyroscope estimation mode is enabled
 *
 * @param value 1 if check enabled, 0 otherwise
 */
void setManualPureGyroEnabled(bool value) {
    if (xSemaphoreTake(angles_mutex, pdMS_TO_TICKS(kMutexMS)) == pdTRUE) {
        filter_context.state.manual_pure_gyro = value;
        (void)xSemaphoreGive(angles_mutex);
    }
}

/**
 * Check whether the manual pure gyroscope estimation mode is enabled
 *
 * @retval true Enabled
 * @retval false Disabled
 */
bool isManualPureGyroEnabled(void) {
    bool enabled = false;

    if (xSemaphoreTake(angles_mutex, pdMS_TO_TICKS(kMutexMS)) == pdTRUE) {
        enabled = filter_context.state.manual_pure_gyro;
        (void)xSemaphoreGive(angles_mutex);
    }

    return enabled;
}

/**
 * Set the display orientation depending on the IMU orientation
 *
 * @param new_orientation New display orientation
 * @retval 0 Success
 * @retval 1 The mutex is not initialised yet
 * @retval 2 Invalid orientation provided
 * @retval 3 Unable to take the orientation mutex
 */
ErrorCode setDisplayOrientation(Orientation new_orientation) {
    if (!orientation_mutex) {
        return createErrorCode(kSetOrientation, 1, kErrorError);
    }

    if (new_orientation >= kNBorientations) {
        return createErrorCode(kSetOrientation, 2, kErrorError);
    }

    if (new_orientation == current_orientation) {
        return kSuccessCode;
    }

    if (xSemaphoreTake(orientation_mutex, kMutexMS) == pdFALSE) {
        return createErrorCode(kSetOrientation, 3, kErrorError);
    }

    current_orientation = new_orientation;
    (void)xSemaphoreGive(orientation_mutex);

    return kSuccessCode;
}

/**
 * Get the display orientation depending on the IMU orientation
 *
 * @param[out] orientation Display orientation
 * @retval 0 Success
 * @retval 1 The mutex is not initialised yet or orientation is nullptr
 * @retval 2 Unable to take the orientation mutex
 */
ErrorCode getDisplayOrientation(Orientation* orientation) {
    if (!orientation_mutex || !orientation) {
        return createErrorCode(kgetOrientation, 1, kErrorError);
    }

    if (xSemaphoreTake(orientation_mutex, pdMS_TO_TICKS(kMutexMS)) == pdFALSE) {
        return createErrorCode(kgetOrientation, 2, kErrorError);
    }

    *orientation = current_orientation;
    (void)xSemaphoreGive(orientation_mutex);

    return kSuccessCode;
}

/**
 * Get the current Mahony filter context
 *
 * @param[out] context Copy of the current context
 * @retval 0 Success
 * @retval 1 NULL context provided
 * @retval 2 Could not take the angles mutex
 */
ErrorCode getMahonyContext(MahonyContext* context) {
    if (!context) {
        return createErrorCode(kGetMahonyContext, 1, kErrorCritical);
    }

    if (xSemaphoreTake(angles_mutex, pdMS_TO_TICKS(kMutexMS)) == pdFALSE) {
        return createErrorCode(kGetMahonyContext, 2, kErrorError);
    }

    *context = filter_context;
    (void)xSemaphoreGive(angles_mutex);

    return kSuccessCode;
}

/**
 * Get the Mahony filter's minimum cosine of the angle between estimated body attitude and measured acceleration
 *
 * @return Minimum alignment cosine
 */
float getMinAlignmentCosine(void) {
    float alignment_cosine = 0.0F;

    if (xSemaphoreTake(angles_mutex, pdMS_TO_TICKS(kMutexMS)) == pdTRUE) {
        alignment_cosine = filter_context.min_alignment_cosine;
        (void)xSemaphoreGive(angles_mutex);
    }

    return alignment_cosine;
}

/**
 * Set the Mahony filter's minimum cosine of the angle between estimated body attitude and measured acceleration
 *
 * @param value Minimum alignment cosine
 */
void setMinAlignmentCosine(float value) {
    if ((value < 0.0F) || isnan(value) || isinf(value)) {
        return;
    }

    if (xSemaphoreTake(angles_mutex, pdMS_TO_TICKS(kMutexMS)) == pdTRUE) {
        filter_context.min_alignment_cosine = value;
        (void)xSemaphoreGive(angles_mutex);
    }
}

/**
 * Get the Mahony filter's maximum deviation from a norm of 1
 *
 * @return Maximum deviation
 */
float getMaxNormDeviation(void) {
    float max_epsilon = 0.0F;

    if (xSemaphoreTake(angles_mutex, pdMS_TO_TICKS(kMutexMS)) == pdTRUE) {
        max_epsilon = filter_context.max_norm_epsilon;
        (void)xSemaphoreGive(angles_mutex);
    }

    return max_epsilon;
}

/**
 * Set the Mahony filter's maximum deviation from a norm of 1
 *
 * @param value Minimum alignment cosine
 */
void setMaxNormDeviation(float value) {
    if ((value < 0.0F) || isnan(value) || isinf(value)) {
        return;
    }

    if (xSemaphoreTake(angles_mutex, pdMS_TO_TICKS(kMutexMS)) == pdTRUE) {
        filter_context.max_norm_epsilon = value;
        (void)xSemaphoreGive(angles_mutex);
    }
}

/**
 * Get the Mahony filter's minimum factor of trust for kP
 *
 * @return Minimum factor
 */
float getMinimumKpTrustFactor(void) {
    float min_factor = 0.0F;

    if (xSemaphoreTake(angles_mutex, pdMS_TO_TICKS(kMutexMS)) == pdTRUE) {
        min_factor = filter_context.min_kp_trust_factor;
        (void)xSemaphoreGive(angles_mutex);
    }

    return min_factor;
}

/**
 * Set the Mahony filter's minimum factor of trust for kP
 *
 * @param value Minimum trust factor
 */
void setMinimumKpTrustFactor(float value) {
    if ((value < 0.0F) || isnan(value) || isinf(value)) {
        return;
    }

    if (xSemaphoreTake(angles_mutex, pdMS_TO_TICKS(kMutexMS)) == pdTRUE) {
        filter_context.min_kp_trust_factor = value;
        (void)xSemaphoreGive(angles_mutex);
    }
}

/****************************************************************************************************************/
/****************************************************************************************************************/

/**
 * Run the IMU state machine
 * 
 * @param argument Unused
 */
static void taskIMU(void* argument) {
    // A large switch is the most straightforward way to ignore funcions that are not states
    // Therefore, Lizard linter can ignore this function's cyclomatic complexity
    // #lizard forgives(cyclomatic_complexity)

    (void)argument;
    while (1) {
        //run the state machine
        switch (imu_state) {
            case kStateStartup:
                result = stateStartup();
                imu_state = kstateConfiguring;
                break;

            case kstateConfiguring:
                result = stateConfiguring();
                imu_state = kStateMeasuring;
                break;

            case kStateMeasuring:
                result = stateMeasuring();
                break;

            case kStateError:
                Error_Handler();
                break;

            case kFunctionTask:
            case kIgnoreSamples:
            case kSetOrientation:
            case kgetOrientation:
            case kGetMahonyContext:
            default:
                result = createErrorCode(kFunctionTask, 0, kErrorCritical);
                break;
        }

        consumeStateMachineError(result);
    };
}

/**
 * State in which the IMU is resetted and the communication is checked
 * 
 * @retval 0 Success
 * @retval 1 Error while checking the communication
 * @retval 2 Error while requesting the soft reset
 * @retval 3 Error while running the accelerometer self-test
 * @retval 4 Error while running the gyroscope self-test
 */
static ErrorCode stateStartup(void) {
    task_notifiable = false;

    vTaskDelay(pdMS_TO_TICKS(kStartupTimeMS));

    result = IMUcheckDeviceID();
    EXIT_ON_ERROR(result, kStateStartup, 1)
    logSerial(kErrorInfo, "IMU communication OK");

    result = IMUsoftReset();
    EXIT_ON_ERROR(result, kStateStartup, 2)
    vTaskDelay(pdMS_TO_TICKS(kStartupTimeMS));
    logSerial(kErrorInfo, "IMU soft-reset done");

    constexpr uint8_t self_test_attempts = 5U;

    //run the accelerometer self-testing
    for (uint8_t attempts = 0; attempts < self_test_attempts; attempts++) {
        result = selfTestAccelerometer();
        if (!isError(result)) {
            logSerial(kErrorInfo, "Accemerometer self-test ok");
            break;
        }
    }
    EXIT_ON_ERROR(result, kStateStartup, 3)

    //run the gyroscope self-testing
    for (uint8_t attempts = 0; attempts < self_test_attempts; attempts++) {
        result = selfTestGyroscope();
        if (!isError(result)) {
            logSerial(kErrorInfo, "Gyroscope self-test ok");
            break;
        }
    }
    EXIT_ON_ERROR(result, kStateStartup, 4)

    return kSuccessCode;
}

/**
 * State in which the IMU is configured
 * 
 * @retval 0 Success
 * @retval 1 Error while initialising the IMU
 * @retval 2 Error while writing the IMU configuration
 * @retval 3 Error while ingoring samples after configuration
 */
static ErrorCode stateConfiguring(void) {
    //run the IMU initial configuration (e.g. power-after-reset procedure)
    result = IMUinitialise();
    EXIT_ON_ERROR(result, kstateConfiguring, 1)

    //write the config to the IMU
    result = IMUconfigure();
    EXIT_ON_ERROR(result, kstateConfiguring, 2)

    task_notifiable = true;

    result = ignoreSamples();
    EXIT_ON_ERROR(result, kstateConfiguring, 3)

    //reset the Mahony filter's persistant variables
    resetMahonyFilter(&filter_context);
    IMUsetupTimebase(&filter_context);

    //TODO allow for samples to be dropped in the LSM6DSO, thus using task notification
    logSerial(kErrorInfo, "IMU and Mahony filter initialisation OK");
    return kSuccessCode;
}

/**
 * Ignore samples after configuration
 *
 * @retval 0 Success
 * @retval 1 Error while waiting for a sample 
 */
static ErrorCode ignoreSamples(void) {
    uint8_t remaining = getNbSamplesToIgnore();
    while (remaining) {
        //wait for a notification indicating a sample is ready
        if (ulTaskNotifyTake(pdTRUE, pdMS_TO_TICKS(kTimeoutMS)) == pdFALSE) {
            return createErrorCode(kIgnoreSamples, 1, kErrorError);
        }

        IMUsample dummy;
        IMUgetSample(&dummy);
        remaining--;
    }

    logSerial(kErrorInfo, "%u IMU samples ignored for synchronisation", getNbSamplesToIgnore());
    return kSuccessCode;
}

/**
 * State in which the IMU is measuring
 * 
 * @retval 0 Success
 * @retval 1 No interrupt received from the IMU in a timely manner
 * @retval 2 Error while getting the latest IMU sample
 * @retval 3 Could not take the angles mutex
 */
static ErrorCode stateMeasuring(void) {
    //wait for measurements to be ready
    if (ulTaskNotifyTake(pdTRUE, pdMS_TO_TICKS(kTimeoutMS)) == pdFALSE) {
        return (createErrorCode(kStateMeasuring, 1, kErrorCritical));
    }

    //get the latest sample
    IMUsample sample;
    result = IMUgetSample(&sample);
    EXIT_ON_ERROR(result, kStateMeasuring, 2)

    static float previous_angles[kNBaxis];
    float current_angles[kNBaxis];
    float deltas[kNBaxis];

    if (xSemaphoreTake(angles_mutex, pdMS_TO_TICKS(kMutexMS)) == pdFALSE) {
        logSerial(kErrorInfo, "Could not take the angles mutex. Skipping update");
        return createErrorCode(kStateMeasuring, 3, kErrorInfo);
    }

    //apply sensor fusion to the measurements
    filter_context.dt.last_sampled_tick = sample.imu_tick;
    if (!updateMahonyFilter(&filter_context, &sample)) {
        (void)xSemaphoreGive(angles_mutex);
        return kSuccessCode;
    }

    //get the current angles
    current_angles[kXaxis] = angleAlongAxis(&filter_context.attitude, kXaxis);
    current_angles[kYaxis] = angleAlongAxis(&filter_context.attitude, kYaxis);
    (void)xSemaphoreGive(angles_mutex);

    //if angles did not change enough, exit
    deltas[kXaxis] = fabsf(previous_angles[kXaxis] - current_angles[kXaxis]);
    deltas[kYaxis] = fabsf(previous_angles[kYaxis] - current_angles[kYaxis]);
    if ((deltas[kXaxis] <= kDegreesTenthsToRadians) && (deltas[kYaxis] <= kDegreesTenthsToRadians)) {
        return kSuccessCode;
    }

    //trigger angles update event
    triggerHardwareEvent(kEventAngle);
    previous_angles[kXaxis] = current_angles[kXaxis];
    previous_angles[kYaxis] = current_angles[kYaxis];

    return kSuccessCode;
}

/**
 * Check if an error occurred in the state machine, log it and set machine error
 *
 * @param code Error code of the last state called
 */
static void consumeStateMachineError(ErrorCode code) {
    if (!isError(code)) {
        return;
    }

    logSerial(code.level, "IMU Error %lx", (unsigned long)code.dword);
    imu_state = kStateError;
}
