gilleshenrard/leany/firmware/hardware/battery/bq25619.h

/**
 * SPDX-FileCopyrightText: 2026 Gilles Henrard <contact@gilleshenrard.com>
 * SPDX-License-Identifier: MIT
 * 
 * @file bq25619.h
 * @author Gilles Henrard
 */
#ifndef HARDWARE_BATTERY_BQ25619_H
#define HARDWARE_BATTERY_BQ25619_H
#include "bq25619_registers.h"
#include "errorstack.h"

ErrorCode testBQ25619identifier(void);
ErrorCode resetBQ25619(void);
ErrorCode configureBQ25619(void);
ErrorCode updateBQ25619status(ChargerStatus* new_status, ChargerStatus* changes);
bool isBQ25619charging(const ChargerStatus* status);
bool BQ25619statusChanged(const ChargerStatus* changes);
bool BQ25619Error(const ChargerStatus* status);
ErrorCode disconnectBattery(void);

#endif
