gilleshenrard/leany/firmware/hardware/imu/lsm6/lsm6dsr_registers.h

/**
 * SPDX-FileCopyrightText: 2026 Gilles Henrard <contact@gilleshenrard.com>
 * SPDX-License-Identifier: MIT
 *
 * @file lsm6_registers.h
 * @details Describe LSM6DSR registers and bit values
 * @author Gilles Henrard
 *
 * @note Datasheet : https://www.st.com/resource/en/datasheet/lsm6dsr.pdf
 */
#ifndef HARDWARE_IMU_LSM6DSR_LSM6DSR_REGISTERS_H_INCLUDED
#define HARDWARE_IMU_LSM6DSR_LSM6DSR_REGISTERS_H_INCLUDED
#include <stdint.h>

// WhoAmI register (0x0F) values
#undef kLSM6_WHOAMI
#define kLSM6_WHOAMI 0x6BU  ///< LSM6DSR Who Am I constant value

typedef enum : uint8_t {
    kS4S_TPH_L = 0x04U,        ///< RW - Sensor synchronization time frame register (LSB)
    kS4S_TPH_H = 0x05U,        ///< RW - Sensor synchronization time frame register (MSB)
    kS4S_RR = 0x06U,           ///< RW - Sensor synchronization resolution ratio register
    kS4S_ST_CMD_CODE = 0x60U,  ///< RW - Sensor synchronization resolution ratio register
    kS4S_DT_REG = 0x61U,       ///< RW - Sensor synchronization resolution ratio register
} LSM6DSRregister;

typedef enum : uint8_t {
    kADV_PEDO = 0x03U,  ///< RW - Enable/disable pedometer advanced features register
} LSM6DSRembeddedFunction;

#endif
