gilleshenrard/leany/firmware/tasks/task_dispatcher.h

/**
 * SPDX-FileCopyrightText: 2026 Gilles Henrard <contact@gilleshenrard.com>
 * SPDX-License-Identifier: MIT
 * 
 * @file task_dispatcher.h
 * @author Gilles Henrard
 */
#ifndef CONTROLLER_DISPATCHER_H
#define CONTROLLER_DISPATCHER_H
#include "errorstack.h"

ErrorCode createMessageDispatchertask(void);
bool setLastErrorCode(ErrorCode error);
bool getLastErrorCode(ErrorCode* error);

#endif
