gilleshenrard/leany/firmware/hardware/gpio/buttons.h

/**
 * SPDX-FileCopyrightText: 2026 Gilles Henrard <contact@gilleshenrard.com>
 * SPDX-License-Identifier: MIT
 * 
 * @file buttons.h
 * @author Gilles Henrard
 */
#ifndef INC_BUTTONS_H
#define INC_BUTTONS_H
#include "errorstack.h"

ErrorCode runButtonsStateMachine(void);

#endif
