gilleshenrard/leany/firmware/tasks/serialtask/scpi_parser.h

/**
 * SPDX-FileCopyrightText: 2026 Gilles Henrard <contact@gilleshenrard.com>
 * SPDX-License-Identifier: MIT
 * 
 * @file scpi_parser.h
 * @author Gilles Henrard
 */
#ifndef HARDWARE_SERIAL_SCPI_PARSER_H
#define HARDWARE_SERIAL_SCPI_PARSER_H
#include <stdint.h>

#include "generic_command.inc"

void resetSCPIparser(void);
uint8_t pushSCPIcharacter(uint8_t new_char, GenericCommand* command_received);

#endif
