gilleshenrard/leany/firmware/utils/hardware_events.h

/**
 * SPDX-FileCopyrightText: 2026 Gilles Henrard <contact@gilleshenrard.com>
 * SPDX-License-Identifier: MIT
 * 
 * @file hardware_events.h
 * @author Gilles Henrard
 */
#ifndef HARDWARE_SYSUTILS_HARDWARE_EVENTS_H
#define HARDWARE_SYSUTILS_HARDWARE_EVENTS_H
#include <FreeRTOS.h>
#include <portmacro.h>
#include <stdint.h>

/**
 * Enumeration of hardware events
 */
// NOLINTBEGIN (readability-enum-initial-value)
typedef enum : uint8_t {
    kEventAngle = 0U,             ///< Event : Angle value change
    kEventZero = 1U,              ///< Event : Zero down measurements
    kEventCancelZero = 2U,        ///< Event : Cancel measurements zeroing
    kEventHold = 3U,              ///< Event : Enable measurements holding
    kEventSerialCommand = 4U,     ///< Event : Command received over serial connection
    kEventOrientation = 5U,       ///< Event : Display orientation changed
    kEventTemperature = 6U,       ///< Event : MCU internal temperature changed
    kEventToggleScreen = 7U,      ///< Event : Toggle screen requested
    kEventBatteryStatus = 8U,     ///< Event : Battery status update
    kEventErrorCode = 9U,         ///< Event : Error detected
    kEventMonitoringCycle = 10U,  ///< Event : Monitoring cycle required
    kNbEvents,                    ///< Number of events handled
} Event;
// NOLINTEND (readability-enum-initial-value)

void createHardwareEventsGroup(void);
void triggerHardwareEvent(Event event);
void triggerHardwareEventFromISR(Event event);
bool isHardwareEventTriggered(Event event);
bool waitForHardwareEvents(TickType_t max_wait_time_ms);
void clearHardwareEvents(void);
#endif
