gilleshenrard/leany/firmware/utils/orientation.h

/**
 * SPDX-FileCopyrightText: 2026 Gilles Henrard <contact@gilleshenrard.com>
 * SPDX-License-Identifier: MIT
 *
 * @file orientation.h
 * @details Describe the different device orientations
 * @author Gilles Henrard
 */
#ifndef INC_HARDWARE_DISPLAY_ORIENTATION_H
#define INC_HARDWARE_DISPLAY_ORIENTATION_H

/**
 * @brief Enumeration of the available display kOrientations
 */
typedef enum : uint8_t {
    kPortrait = 0,   ///< Portrait
    kPortrait180,    ///< Portrait, rotated 180°
    kLandscape,      ///< Landscape
    kLandscape180,   ///< Landscape, rotated 180°
    kNBorientations  ///< Number of available kOrientations
} Orientation;

#endif
